clintondsza/oniondao-badge/software/mods/pin-test/components/GxEPD2/other/GxEPD2_420_SE0420NQ04.cpp

// Display Library for SPI e-paper panels from Dalian Good Display and boards from Waveshare.
// Requires HW SPI and Adafruit_GFX. Caution: these e-papers require 3.3V supply AND data lines!
//
// based on Demo Example from Good Display: http://www.e-paper-display.com/download_list/downloadcategoryid=34&isMode=false.html
// Panel: SE0420NQ04 : origin unknown
// Controller: UC8276C : found here : https://www.laskakit.cz/user/related_files/uc8276.pdf or https://github.com/CursedHardware/epd-driver-ic
//
// Author: Jean-Marc Zingg
//
// Version: see library.properties
//
// Library: https://github.com/ZinggJM/GxEPD2

#include "GxEPD2_420_SE0420NQ04.h"

GxEPD2_420_SE0420NQ04::GxEPD2_420_SE0420NQ04(int16_t cs, int16_t dc, int16_t rst, int16_t busy) :
  GxEPD2_EPD(cs, dc, rst, busy, LOW, 10000000, WIDTH, HEIGHT, panel, hasColor, hasPartialUpdate, hasFastPartialUpdate)
{
}

void GxEPD2_420_SE0420NQ04::clearScreen(uint8_t value)
{
  writeScreenBuffer(value);
  refresh(true);
  writeScreenBuffer(value);
}

void GxEPD2_420_SE0420NQ04::writeScreenBuffer(uint8_t value)
{
  _initial_write = false; // initial full screen buffer clean done
  if (!_using_partial_mode) _Init_Part();
  if (_initial_refresh)
  {
    _writeCommand(0x10); // init old data
    _startTransfer();
    for (uint32_t i = 0; i < uint32_t(WIDTH) * uint32_t(HEIGHT) / 8; i++)
    {
      _transfer(value);
    }
    _endTransfer();
  }
  _writeCommand(0x13);
  _startTransfer();
  for (uint32_t i = 0; i < uint32_t(WIDTH) * uint32_t(HEIGHT) / 8; i++)
  {
    _transfer(value);
  }
  _endTransfer();
}

void GxEPD2_420_SE0420NQ04::writeImage(const uint8_t bitmap[], int16_t x, int16_t y, int16_t w, int16_t h, bool invert, bool mirror_y, bool pgm)
{
  if (_initial_write) writeScreenBuffer(); // initial full screen buffer clean
  delay(1); // yield() to avoid WDT on ESP8266 and ESP32
  int16_t wb = (w + 7) / 8; // width bytes, bitmaps are padded
  x -= x % 8; // byte boundary
  w = wb * 8; // byte boundary
  int16_t x1 = x < 0 ? 0 : x; // limit
  int16_t y1 = y < 0 ? 0 : y; // limit
  int16_t w1 = x + w < int16_t(WIDTH) ? w : int16_t(WIDTH) - x; // limit
  int16_t h1 = y + h < int16_t(HEIGHT) ? h : int16_t(HEIGHT) - y; // limit
  int16_t dx = x1 - x;
  int16_t dy = y1 - y;
  w1 -= dx;
  h1 -= dy;
  if ((w1 <= 0) || (h1 <= 0)) return;
  if (!_using_partial_mode) _Init_Part();
  //uint32_t start = micros();
  _writeCommand(0x91); // partial in
  _setPartialRamArea(x1, y1, w1, h1);
  _writeCommand(0x13);
  _startTransfer();
  for (int16_t i = 0; i < h1; i++)
  {
    for (int16_t j = 0; j < w1 / 8; j++)
    {
      uint8_t data;
      // use wb, h of bitmap for index!
      int16_t idx = mirror_y ? j + dx / 8 + ((h - 1 - (i + dy))) * wb : j + dx / 8 + (i + dy) * wb;
      if (pgm)
      {
#if defined(__AVR) || defined(ESP8266) || defined(ESP32)
        data = pgm_read_byte(&bitmap[idx]);
#else
        data = bitmap[idx];
#endif
      }
      else
      {
        data = bitmap[idx];
      }
      if (invert) data = ~data;
      _transfer(data);
    }
  }
  _endTransfer();
  _writeCommand(0x92); // partial out
  //Serial.print("GxEPD2_420_SE0420NQ04::writeImage took "); Serial.println(micros() - start);
  delay(1); // yield() to avoid WDT on ESP8266 and ESP32
}

void GxEPD2_420_SE0420NQ04::writeImagePart(const uint8_t bitmap[], int16_t x_part, int16_t y_part, int16_t w_bitmap, int16_t h_bitmap,
    int16_t x, int16_t y, int16_t w, int16_t h, bool invert, bool mirror_y, bool pgm)
{
  if (_initial_write) writeScreenBuffer(); // initial full screen buffer clean
  delay(1); // yield() to avoid WDT on ESP8266 and ESP32
  if ((w_bitmap < 0) || (h_bitmap < 0) || (w < 0) || (h < 0)) return;
  if ((x_part < 0) || (x_part >= w_bitmap)) return;
  if ((y_part < 0) || (y_part >= h_bitmap)) return;
  int16_t wb_bitmap = (w_bitmap + 7) / 8; // width bytes, bitmaps are padded
  x_part -= x_part % 8; // byte boundary
  w = w_bitmap - x_part < w ? w_bitmap - x_part : w; // limit
  h = h_bitmap - y_part < h ? h_bitmap - y_part : h; // limit
  x -= x % 8; // byte boundary
  w = 8 * ((w + 7) / 8); // byte boundary, bitmaps are padded
  int16_t x1 = x < 0 ? 0 : x; // limit
  int16_t y1 = y < 0 ? 0 : y; // limit
  int16_t w1 = x + w < int16_t(WIDTH) ? w : int16_t(WIDTH) - x; // limit
  int16_t h1 = y + h < int16_t(HEIGHT) ? h : int16_t(HEIGHT) - y; // limit
  int16_t dx = x1 - x;
  int16_t dy = y1 - y;
  w1 -= dx;
  h1 -= dy;
  if ((w1 <= 0) || (h1 <= 0)) return;
  if (!_using_partial_mode) _Init_Part();
  _writeCommand(0x91); // partial in
  _setPartialRamArea(x1, y1, w1, h1);
  _writeCommand(0x13);
  _startTransfer();
  for (int16_t i = 0; i < h1; i++)
  {
    for (int16_t j = 0; j < w1 / 8; j++)
    {
      uint8_t data;
      // use wb_bitmap, h_bitmap of bitmap for index!
      int16_t idx = mirror_y ? x_part / 8 + j + dx / 8 + ((h_bitmap - 1 - (y_part + i + dy))) * wb_bitmap : x_part / 8 + j + dx / 8 + (y_part + i + dy) * wb_bitmap;
      if (pgm)
      {
#if defined(__AVR) || defined(ESP8266) || defined(ESP32)
        data = pgm_read_byte(&bitmap[idx]);
#else
        data = bitmap[idx];
#endif
      }
      else
      {
        data = bitmap[idx];
      }
      if (invert) data = ~data;
      _transfer(data);
    }
  }
  _endTransfer();
  _writeCommand(0x92); // partial out
  delay(1); // yield() to avoid WDT on ESP8266 and ESP32
}

void GxEPD2_420_SE0420NQ04::writeImage(const uint8_t* black, const uint8_t* color, int16_t x, int16_t y, int16_t w, int16_t h, bool invert, bool mirror_y, bool pgm)
{
  if (black)
  {
    writeImage(black, x, y, w, h, invert, mirror_y, pgm);
  }
}

void GxEPD2_420_SE0420NQ04::writeImagePart(const uint8_t* black, const uint8_t* color, int16_t x_part, int16_t y_part, int16_t w_bitmap, int16_t h_bitmap,
    int16_t x, int16_t y, int16_t w, int16_t h, bool invert, bool mirror_y, bool pgm)
{
  if (black)
  {
    writeImagePart(black, x_part, y_part, w_bitmap, h_bitmap, x, y, w, h, invert, mirror_y, pgm);
  }
}

void GxEPD2_420_SE0420NQ04::writeNative(const uint8_t* data1, const uint8_t* data2, int16_t x, int16_t y, int16_t w, int16_t h, bool invert, bool mirror_y, bool pgm)
{
  if (data1)
  {
    writeImage(data1, x, y, w, h, invert, mirror_y, pgm);
  }
}

void GxEPD2_420_SE0420NQ04::drawImage(const uint8_t bitmap[], int16_t x, int16_t y, int16_t w, int16_t h, bool invert, bool mirror_y, bool pgm)
{
  writeImage(bitmap, x, y, w, h, invert, mirror_y, pgm);
  refresh(x, y, w, h);
  writeImage(bitmap, x, y, w, h, invert, mirror_y, pgm);
}

void GxEPD2_420_SE0420NQ04::drawImagePart(const uint8_t bitmap[], int16_t x_part, int16_t y_part, int16_t w_bitmap, int16_t h_bitmap,
    int16_t x, int16_t y, int16_t w, int16_t h, bool invert, bool mirror_y, bool pgm)
{
  writeImagePart(bitmap, x_part, y_part, w_bitmap, h_bitmap, x, y, w, h, invert, mirror_y, pgm);
  refresh(x, y, w, h);
  writeImagePart(bitmap, x_part, y_part, w_bitmap, h_bitmap, x, y, w, h, invert, mirror_y, pgm);
}

void GxEPD2_420_SE0420NQ04::drawImage(const uint8_t* black, const uint8_t* color, int16_t x, int16_t y, int16_t w, int16_t h, bool invert, bool mirror_y, bool pgm)
{
  writeImage(black, color, x, y, w, h, invert, mirror_y, pgm);
  refresh(x, y, w, h);
  writeImage(black, color, x, y, w, h, invert, mirror_y, pgm);
}

void GxEPD2_420_SE0420NQ04::drawImagePart(const uint8_t* black, const uint8_t* color, int16_t x_part, int16_t y_part, int16_t w_bitmap, int16_t h_bitmap,
    int16_t x, int16_t y, int16_t w, int16_t h, bool invert, bool mirror_y, bool pgm)
{
  writeImagePart(black, color, x_part, y_part, w_bitmap, h_bitmap, x, y, w, h, invert, mirror_y, pgm);
  refresh(x, y, w, h);
  writeImagePart(black, color, x_part, y_part, w_bitmap, h_bitmap, x, y, w, h, invert, mirror_y, pgm);
}

void GxEPD2_420_SE0420NQ04::drawNative(const uint8_t* data1, const uint8_t* data2, int16_t x, int16_t y, int16_t w, int16_t h, bool invert, bool mirror_y, bool pgm)
{
  writeNative(data1, data2, x, y, w, h, invert, mirror_y, pgm);
  refresh(x, y, w, h);
  writeNative(data1, data2, x, y, w, h, invert, mirror_y, pgm);
}

void GxEPD2_420_SE0420NQ04::refresh(bool partial_update_mode)
{
  if (partial_update_mode) refresh(0, 0, WIDTH, HEIGHT);
  else
  {
    if (_using_partial_mode) _Init_Full();
    _Update_Full();
    _initial_refresh = false; // initial full update done
  }
}

void GxEPD2_420_SE0420NQ04::refresh(int16_t x, int16_t y, int16_t w, int16_t h)
{
  if (_initial_refresh) return refresh(false); // initial update needs be full update
  // intersection with screen
  int16_t w1 = x < 0 ? w + x : w; // reduce
  int16_t h1 = y < 0 ? h + y : h; // reduce
  int16_t x1 = x < 0 ? 0 : x; // limit
  int16_t y1 = y < 0 ? 0 : y; // limit
  w1 = x1 + w1 < int16_t(WIDTH) ? w1 : int16_t(WIDTH) - x1; // limit
  h1 = y1 + h1 < int16_t(HEIGHT) ? h1 : int16_t(HEIGHT) - y1; // limit
  if ((w1 <= 0) || (h1 <= 0)) return;
  // make x1, w1 multiple of 8
  w1 += x1 % 8;
  if (w1 % 8 > 0) w1 += 8 - w1 % 8;
  x1 -= x1 % 8;
  if (!_using_partial_mode) _Init_Part();
  if (usePartialUpdateWindow) _writeCommand(0x91); // partial in
  _setPartialRamArea(x1, y1, w1, h1);
  _Update_Part();
  if (usePartialUpdateWindow) _writeCommand(0x92); // partial out
}

void GxEPD2_420_SE0420NQ04::powerOff(void)
{
  _PowerOff();
}

void GxEPD2_420_SE0420NQ04::hibernate()
{
  _PowerOff();
  if (_rst >= 0)
  {
    _writeCommand(0x07); // deep sleep
    _writeData(0xA5);    // check code
    _hibernating = true;
  }
}

void GxEPD2_420_SE0420NQ04::_setPartialRamArea(uint16_t x, uint16_t y, uint16_t w, uint16_t h)
{
  uint16_t xe = (x + w - 1) | 0x0007; // byte boundary inclusive (last byte)
  uint16_t ye = y + h - 1;
  x &= 0xFFF8; // byte boundary
  _writeCommand(0x90); // partial window
  _writeData(x / 256);
  _writeData(x % 256);
  _writeData(xe / 256);
  _writeData(xe % 256);
  _writeData(y / 256);
  _writeData(y % 256);
  _writeData(ye / 256);
  _writeData(ye % 256);
  _writeData(0x01); // don't see any difference
  //_writeData(0x00); // don't see any difference
}

void GxEPD2_420_SE0420NQ04::_PowerOn()
{
  if (!_power_is_on)
  {
    _writeCommand(0x04);
    _waitWhileBusy("_PowerOn", power_on_time);
  }
  _power_is_on = true;
}

void GxEPD2_420_SE0420NQ04::_PowerOff()
{
  if (_power_is_on)
  {
    _writeCommand(0x02); // power off
    _waitWhileBusy("_PowerOff", power_off_time);
  }
  _power_is_on = false;
  _using_partial_mode = false;
}

void GxEPD2_420_SE0420NQ04::_InitDisplay()
{
  if (_hibernating) _reset();
  _writeCommand(0x00);
  _writeData(0x3F); //bit 3:Gate scan direction  bit 2:Source shift direction;
  _writeData(0xca);
  _writeCommand(0x01);
  _writeData(0x03);
  _writeData(0x10);
  _writeData(0x3f);
  _writeData(0x3f);
  _writeData(0x03);
  _writeCommand(0x06);
  _writeData(0xE7);
  _writeData(0xE7);
  _writeData(0x3D);
  _writeCommand(0X60); // TCON SETTING  (TCON)
  _writeData(0x22);
  _writeCommand(0x82); // vcom
  _writeData(0x00);
  _writeCommand(0x30); //
  _writeData(0x09);    //   50HZ
  _writeCommand(0xE3); //
  _writeData(0x88);    //
  _writeCommand(0x61); // Resolution setting
  _writeData(0x01);
  _writeData(0x90);
  _writeData(0x01);
  _writeData(0x2C);
  _writeCommand (0x50); // Border
  _writeData(0xb7);     // white
}

// full update waveform (taken form GxEPD2_420, adapted for UC8276C)

const unsigned char GxEPD2_420_SE0420NQ04::lut_20_vcom0_full[] PROGMEM =
{
  0x01, 0x08, 0x00, 0x00, 0x00, 0x02, 0x00,
  //0x60, 0x28, 0x28, 0x00, 0x00, 0x01, 0x00,
  0x01, 0x40 + 0x28, 0x80 + 0x28, 0x00, 0x00, 0x01, 0x00,
  0x01, 0x14, 0x00, 0x00, 0x00, 0x01, 0x00,
  0x01, 0x12, 0x12, 0x00, 0x00, 0x01, 0x00,
};

const unsigned char GxEPD2_420_SE0420NQ04::lut_21_ww_full[] PROGMEM =
{
  // 0x40, 0x08, 0x00, 0x00, 0x00, 0x02,
  0x01, 0x40 + 0x08, 0x00, 0x00, 0x00, 0x02, 0x00,
  // 0x90, 0x28, 0x28, 0x00, 0x00, 0x01,
  0x01, 0x80 + 0x28, 0x40 + 0x28, 0x00, 0x00, 0x01, 0x00,
  // 0x40, 0x14, 0x00, 0x00, 0x00, 0x01,
  0x01, 0x40 + 0x14, 0x00, 0x00, 0x00, 0x01, 0x00,
  // 0xA0, 0x12, 0x12, 0x00, 0x00, 0x01,
  0x01, 0x80 + 0x12, 0x80 + 0x12, 0x00, 0x00, 0x01, 0x00,
};

const unsigned char GxEPD2_420_SE0420NQ04::lut_22_bw_full[] PROGMEM =
{
  // 0x40, 0x08, 0x00, 0x00, 0x00, 0x02,
  0x01, 0x40 + 0x08, 0x00, 0x00, 0x00, 0x02, 0x00,
  // 0x90, 0x28, 0x28, 0x00, 0x00, 0x01,
  0x01, 0x80 + 0x28, 0x40 + 0x28, 0x00, 0x00, 0x01, 0x00,
  // 0x40, 0x14, 0x00, 0x00, 0x00, 0x01,
  0x01, 0x40 + 0x14, 0x00, 0x00, 0x00, 0x01, 0x00,
  // 0xA0, 0x12, 0x12, 0x00, 0x00, 0x01,
  0x01, 0x80 + 0x12, 0x80 + 0x12, 0x00, 0x00, 0x01, 0x00,
};

const unsigned char GxEPD2_420_SE0420NQ04::lut_23_wb_full[] PROGMEM =
{
  // 0x80, 0x08, 0x00, 0x00, 0x00, 0x02,
  0x01, 0x80 + 0x08, 0x00, 0x00, 0x00, 0x02, 0x00,
  // 0x90, 0x28, 0x28, 0x00, 0x00, 0x01,
  0x01, 0x80 + 0x28, 0x40 + 0x28, 0x00, 0x00, 0x01, 0x00,
  // 0x80, 0x14, 0x00, 0x00, 0x00, 0x01,
  0x01, 0x80 + 0x14, 0x00, 0x00, 0x00, 0x01, 0x00,
  // 0x50, 0x12, 0x12, 0x00, 0x00, 0x01,
  0x01, 0x40 + 0x12, 0x40 + 0x12, 0x00, 0x00, 0x01, 0x00,
};

const unsigned char GxEPD2_420_SE0420NQ04::lut_24_bb_full[] PROGMEM =
{
  // 0x80, 0x08, 0x00, 0x00, 0x00, 0x02,
  0x01, 0x80 + 0x08, 0x00, 0x00, 0x00, 0x02, 0x00,
  // 0x90, 0x28, 0x28, 0x00, 0x00, 0x01,
  0x01, 0x80 + 0x28, 0x40 + 0x28, 0x00, 0x00, 0x01, 0x00,
  // 0x80, 0x14, 0x00, 0x00, 0x00, 0x01,
  0x01, 0x80 + 0x14, 0x00, 0x00, 0x00, 0x01, 0x00,
  // 0x50, 0x12, 0x12, 0x00, 0x00, 0x01,
  0x01, 0x40 + 0x12, 0x40 + 0x12, 0x00, 0x00, 0x01, 0x00,
};

// partial update waveform (taken form GxEPD2_420, adapted for UC8276C)

// same waveform as by demo code from Good Display
//#define T1  0 // color change charge balance pre-phase
//#define T2  0 // color change or sustain charge balance pre-phase
//#define T3  0 // color change or sustain phase
//#define T4 25 // color change phase

// new waveform created by Jean-Marc Zingg for the actual panel
#define T1 25 // color change charge balance pre-phase
#define T2  1 // color change or sustain charge balance pre-phase
#define T3  4 // color change or sustain phase, was 2 before
#define T4 25 // color change phase

// for new waveform without sustain phase: uncomment next 2 lines, not good for fat fonts
//#define T2  0 // color change or sustain charge balance pre-phase // 0 no sustain
//#define T3  0 // color change or sustain phase // 0 no sustain

// "balanced flash once" variant
//#define T1  0 // color change charge balance pre-phase
//#define T2 25 // color change or sustain charge balance pre-phase
//#define T3 25 // color change or sustain phase
//#define T4  0 // color change phase

const unsigned char GxEPD2_420_SE0420NQ04::lut_20_vcom0_partial[] PROGMEM =
{
  // LUT format of UC8176
  // 0x00, T1, T2, T3, T4, 1, // 00 00 00 00
  // 0x00,  1,  0,  0,  0, 1, // gnd phase
  //
  // LUT format of UC8276
  0x01, // Group Repeat Times
  0x00 + T1,
  0x00 + T2,
  0x00 + T3,
  0x00 + T4,
  0x01, // State 1 repeat times
  0x00, // State 2 repeat times
  0x01, 0x01, 0x00, 0x00, 0x00, 0x01, 0x00, // gnd phase
};

const unsigned char GxEPD2_420_SE0420NQ04::lut_21_ww_partial[] PROGMEM =
{
  // LUT format of UC8176
  // 10 w
  // 0x18, T1, T2, T3, T4, 1, // 00 01 10 00
  // 0x00,  1,  0,  0,  0, 1, // gnd phase
  //
  // LUT format of UC8276
  // 00b : 0V, 01b : VSH, 10b : VSL, 11b : VDHR
  0x01, 0x00 + T1, 0x80 + T2, 0x40 + T3, 0x00 + T4, 0x01, 0x00,
  0x01, 0x01, 0x00, 0x00, 0x00, 0x01, 0x00, // gnd phase
};

const unsigned char GxEPD2_420_SE0420NQ04::lut_22_bw_partial[] PROGMEM =
{
  // LUT format of UC8176
  // 10 w
  // 0x5A, T1, T2, T3, T4, 1, // 01 01 10 10
  // 0x00,  1,  0,  0,  0, 1, // gnd phase
  //
  // LUT format of UC8276
  // 00b : 0V, 01b : VSH, 10b : VSL, 11b : VDHR
  0x01, 0x80 + T1, 0x80 + T2, 0x40 + T3, 0x40 + T4, 0x01, 0x00,
  0x01, 0x01, 0x00, 0x00, 0x00, 0x01, 0x00, // gnd phase
};

const unsigned char GxEPD2_420_SE0420NQ04::lut_23_wb_partial[] PROGMEM =
{
  // LUT format of UC8176
  // 01 b
  // 0xA5, T1, T2, T3, T4, 1, // 10 10 01 01
  // 0x00,  1,  0,  0,  0, 1, // gnd phase
  //
  // LUT format of UC8276
  // 00b : 0V, 01b : VSH, 10b : VSL, 11b : VDHR
  0x01, 0x40 + T1, 0x40 + T2, 0x80 + T3, 0x80 + T4, 0x01, 0x00,
  0x01, 0x01, 0x00, 0x00, 0x00, 0x01, 0x00, // gnd phase
};

const unsigned char GxEPD2_420_SE0420NQ04::lut_24_bb_partial[] PROGMEM =
{
  // LUT format of UC8176
  // 01 b
  // 0x24, T1, T2, T3, T4, 1, // 00 10 01 00
  // 0x00,  1,  0,  0,  0, 1, // gnd phase
  //
  // LUT format of UC8276
  // 00b : 0V, 01b : VSH, 10b : VSL, 11b : VDHR
  0x01, 0x00 + T1, 0x40 + T2, 0x80 + T3, 0x00 + T4, 0x01, 0x00, // State 2 repeat times
  0x01, 0x01, 0x00, 0x00, 0x00, 0x01, 0x00, // gnd phase
};

void GxEPD2_420_SE0420NQ04::_Init_Full()
{
  //  Serial.print("sizeof(lut_20_vcom0_full) "); Serial.println(sizeof(lut_20_vcom0_full));
  //  Serial.print("sizeof(lut_21_ww_full) "); Serial.println(sizeof(lut_21_ww_full));
  //  Serial.print("sizeof(lut_22_bw_full) "); Serial.println(sizeof(lut_22_bw_full));
  //  Serial.print("sizeof(lut_23_wb_full) "); Serial.println(sizeof(lut_23_wb_full));
  //  Serial.print("sizeof(lut_24_bb_full) "); Serial.println(sizeof(lut_24_bb_full));
  _InitDisplay();
  _writeCommand(0x20);
  _writeDataPGM(lut_20_vcom0_full, sizeof(lut_20_vcom0_full), 56 - sizeof(lut_20_vcom0_full));
  _writeCommand(0x21);
  _writeDataPGM(lut_21_ww_full, sizeof(lut_21_ww_full), 42 - sizeof(lut_21_ww_full));
  _writeCommand(0x22);
  _writeDataPGM(lut_22_bw_full, sizeof(lut_22_bw_full), 56 - sizeof(lut_22_bw_full));
  _writeCommand(0x23);
  _writeDataPGM(lut_23_wb_full, sizeof(lut_23_wb_full), 56 - sizeof(lut_23_wb_full));
  _writeCommand(0x24);
  _writeDataPGM(lut_24_bb_full, sizeof(lut_24_bb_full), 56 - sizeof(lut_24_bb_full));
  _PowerOn();
  _using_partial_mode = false;
}

void GxEPD2_420_SE0420NQ04::_Init_Part()
{
  _InitDisplay();
  _writeCommand(0x20);
  _writeDataPGM(lut_20_vcom0_partial, sizeof(lut_20_vcom0_partial), 56 - sizeof(lut_20_vcom0_partial));
  _writeCommand(0x21);
  _writeDataPGM(lut_21_ww_partial, sizeof(lut_21_ww_partial), 42 - sizeof(lut_21_ww_partial));
  _writeCommand(0x22);
  _writeDataPGM(lut_22_bw_partial, sizeof(lut_22_bw_partial), 56 - sizeof(lut_22_bw_partial));
  _writeCommand(0x23);
  _writeDataPGM(lut_23_wb_partial, sizeof(lut_23_wb_partial), 56 - sizeof(lut_23_wb_partial));
  _writeCommand(0x24);
  _writeDataPGM(lut_24_bb_partial, sizeof(lut_24_bb_partial), 56 - sizeof(lut_24_bb_partial));
  _writeCommand (0x50); // Border
  _writeData(0x37);     // floating
  _PowerOn();
  _using_partial_mode = true;
}

void GxEPD2_420_SE0420NQ04::_Update_Full()
{
  _writeCommand(0x12); //display refresh
  _waitWhileBusy("_Update_Full", full_refresh_time);
}

void GxEPD2_420_SE0420NQ04::_Update_Part()
{
  _writeCommand(0x12); //display refresh
  _waitWhileBusy("_Update_Part", partial_refresh_time);
}
